SantaClawzzz/RCXD/Mechanics/Car/Front Wheels and Servo/Servo vasak kinnitus.step

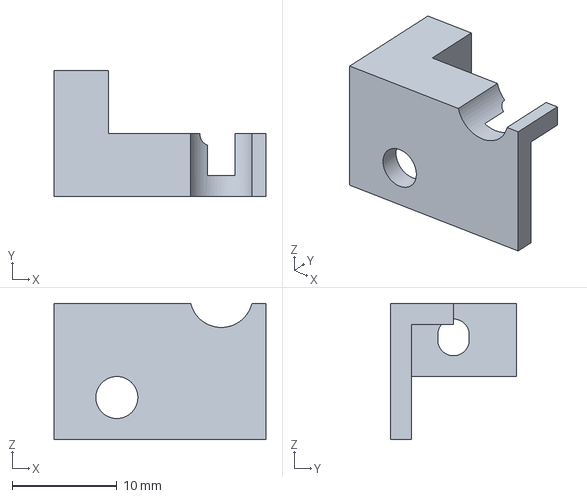
[picture p17: CAD file, 2026-05-07]
Mechanics/Car/Front Wheels and Servo/Servo vasak kinnitus.step
20.2 x 12.0 x 13.0 mm
