SantaClawzzz/RCXD/Mechanics/Car/Front Wheels and Servo/Servo liigend.step

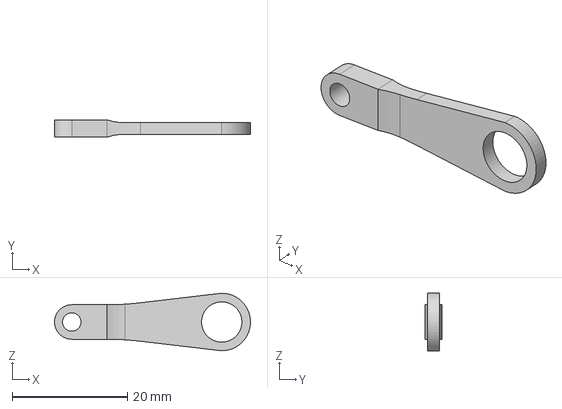
[picture p18: CAD file, 2026-05-07]
Mechanics/Car/Front Wheels and Servo/Servo liigend.step
34.0 x 3.00 x 10.0 mm
