SantaClawzzz/RCXD/Mechanics/Car/Front Wheels and Servo/Esiratta rumm.step

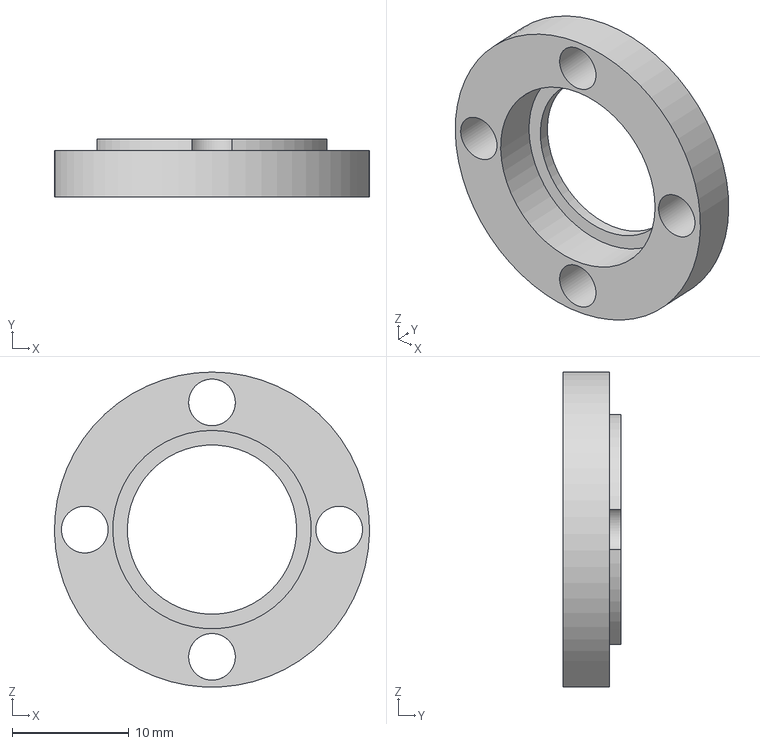
[picture p19: CAD file, 2026-05-07]
Mechanics/Car/Front Wheels and Servo/Esiratta rumm.step
27.0 x 5.00 x 27.0 mm
