SantaClawzzz/RCXD/Mechanics/Car/Front Wheels and Servo/Esiratta kork.step

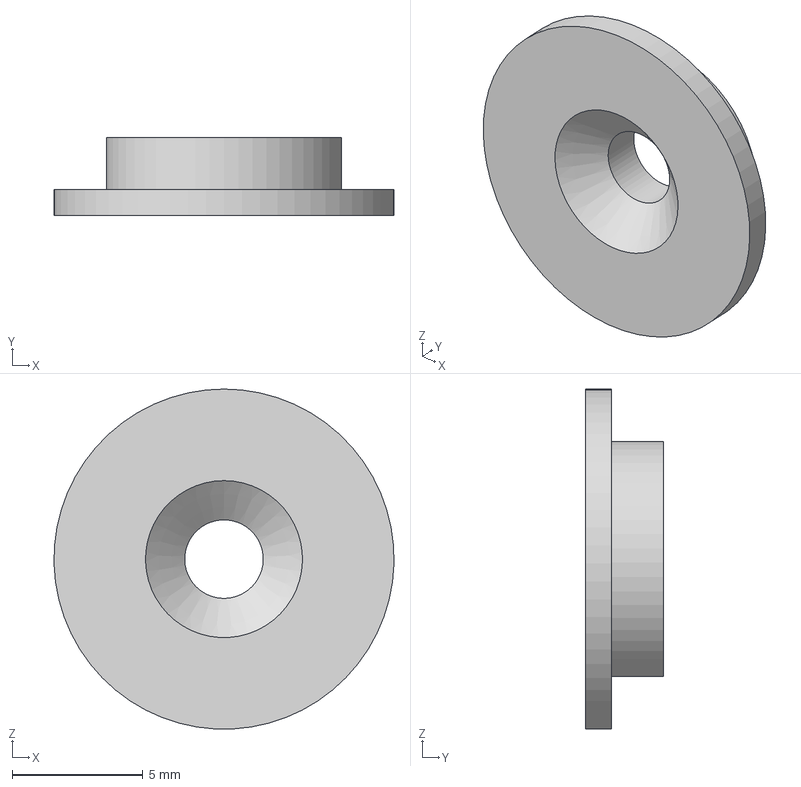
[picture p20: CAD file, 2026-05-07]
Mechanics/Car/Front Wheels and Servo/Esiratta kork.step
13.0 x 3.00 x 13.0 mm
