SantaClawzzz/RCXD/Mechanics/Car/Front Wheels and Servo/Servomootori kinnitus.step

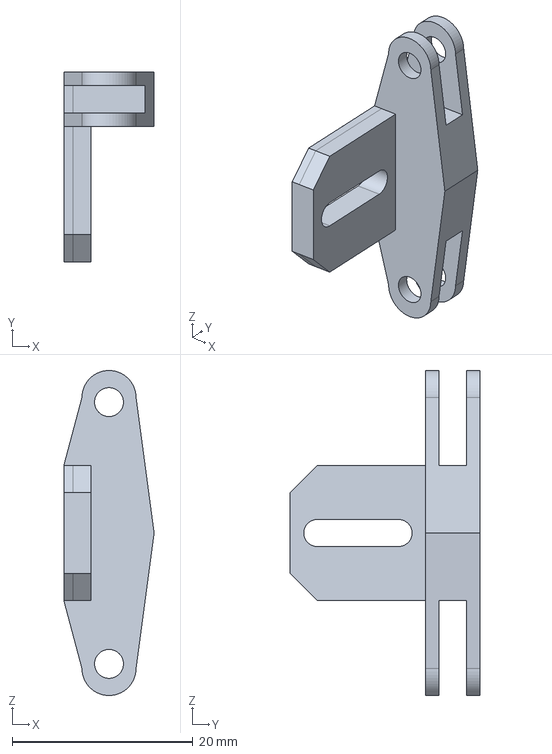
[picture p21: CAD file, 2026-05-07]
Mechanics/Car/Front Wheels and Servo/Servomootori kinnitus.step
10.00 x 21.0 x 36.0 mm
