SantaClawzzz/RCXD/Mechanics/Car/Front Wheels and Servo/Esiratas.step

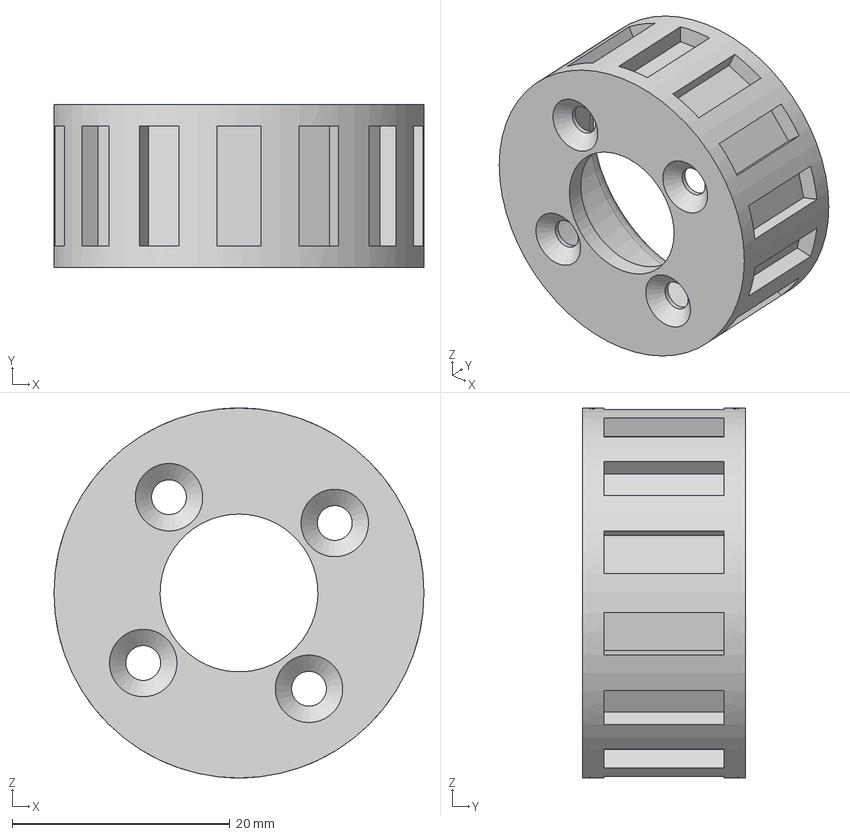
[picture p22: CAD file, 2026-05-07]
Mechanics/Car/Front Wheels and Servo/Esiratas.step
34.0 x 15.0 x 34.0 mm
