SantaClawzzz/RCXD/Mechanics/Car/Front Wheels and Servo/Rattarummi kinnitus.step

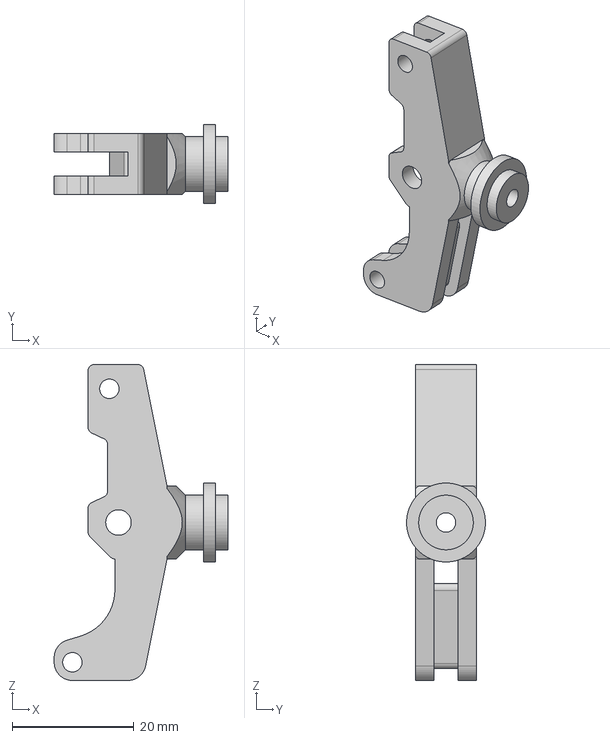
[picture p23: CAD file, 2026-05-07]
Mechanics/Car/Front Wheels and Servo/Rattarummi kinnitus.step
28.6 x 13.0 x 52.0 mm
