SantaClawzzz/RCXD/Mechanics/Car/Front Wheels and Servo/Esirataste hoidik.step

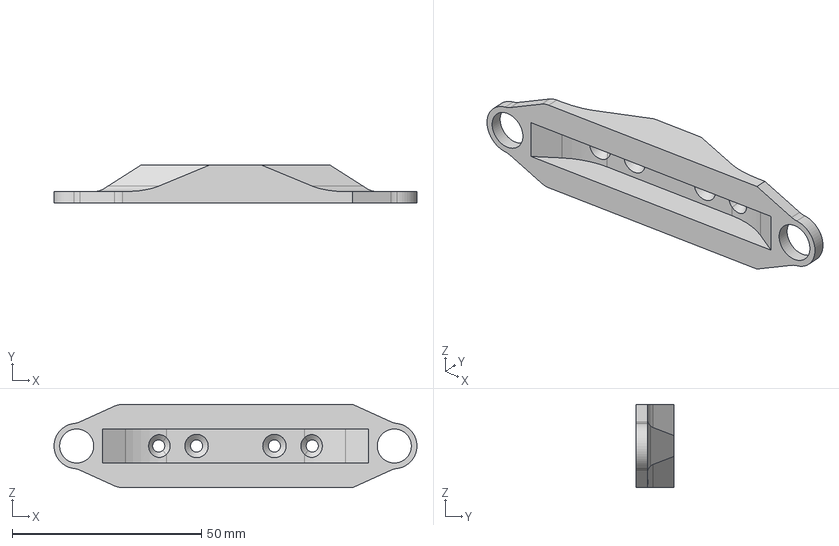
[picture p24: CAD file, 2026-05-07]
Mechanics/Car/Front Wheels and Servo/Esirataste hoidik.step
96.0 x 10.0 x 22.0 mm
