SantaClawzzz/RCXD/Electronics/RC-XD(RX)/RC-XD(RX).pdf

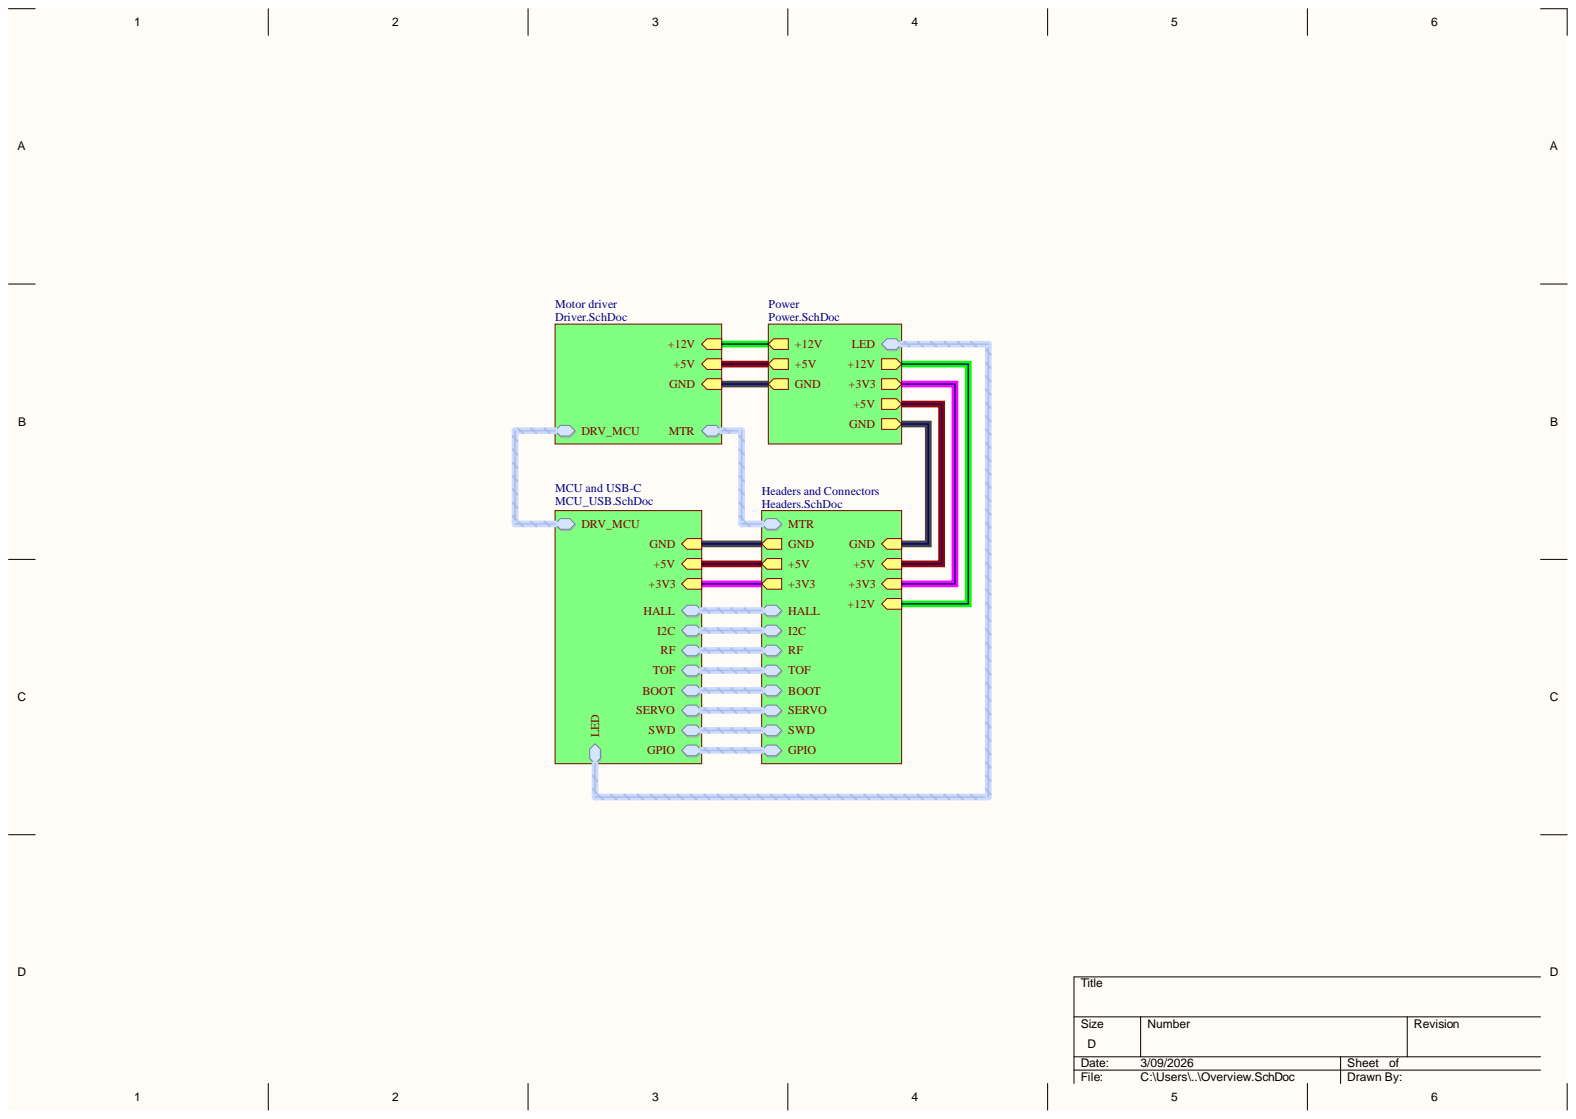
[picture p28: page 1]

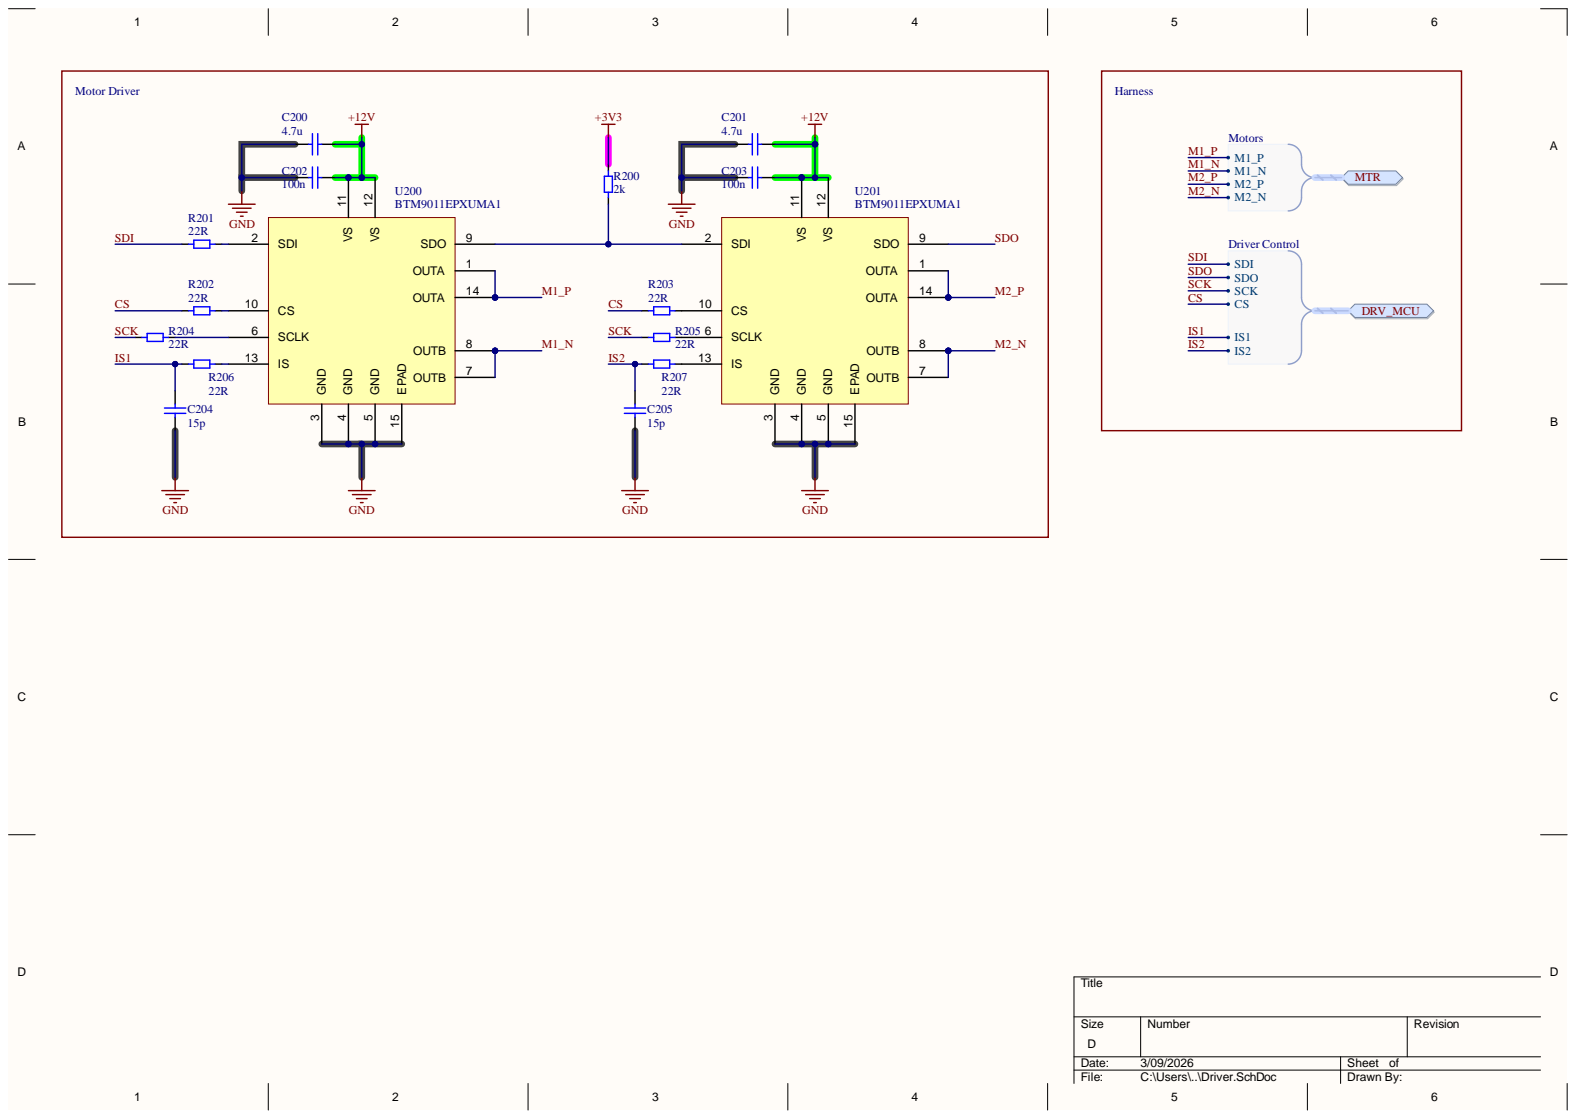
[picture p29: page 2]

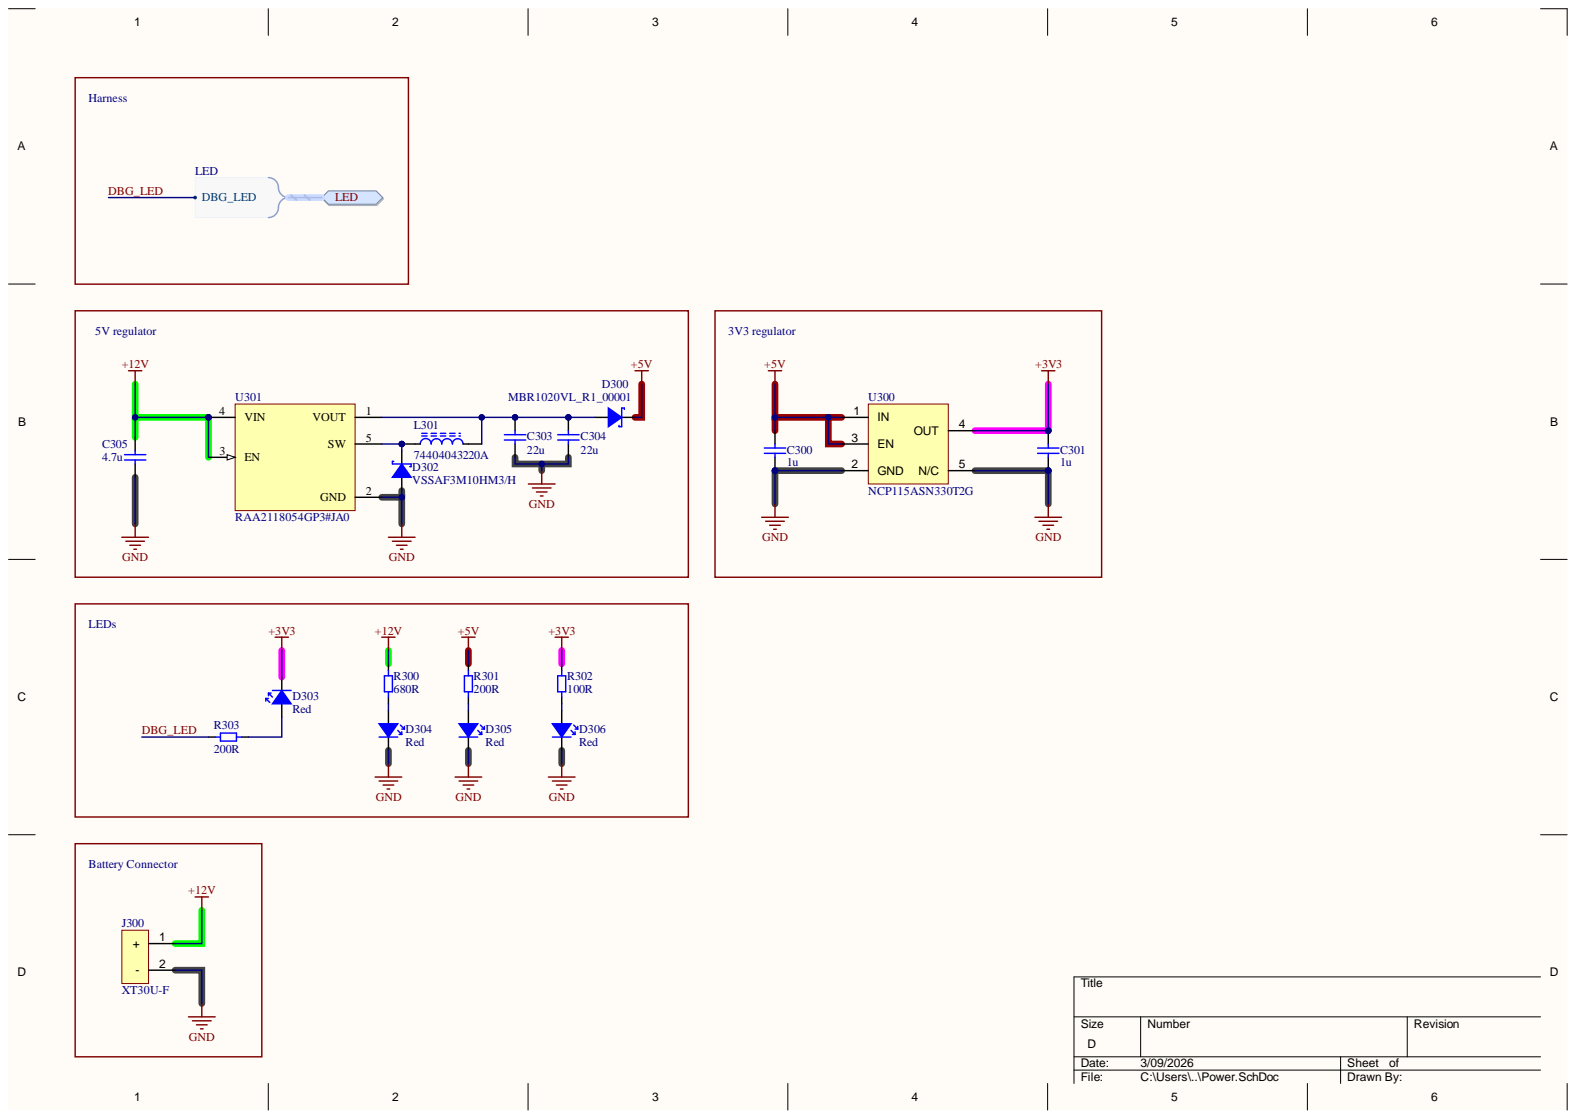
[picture p30: page 3]

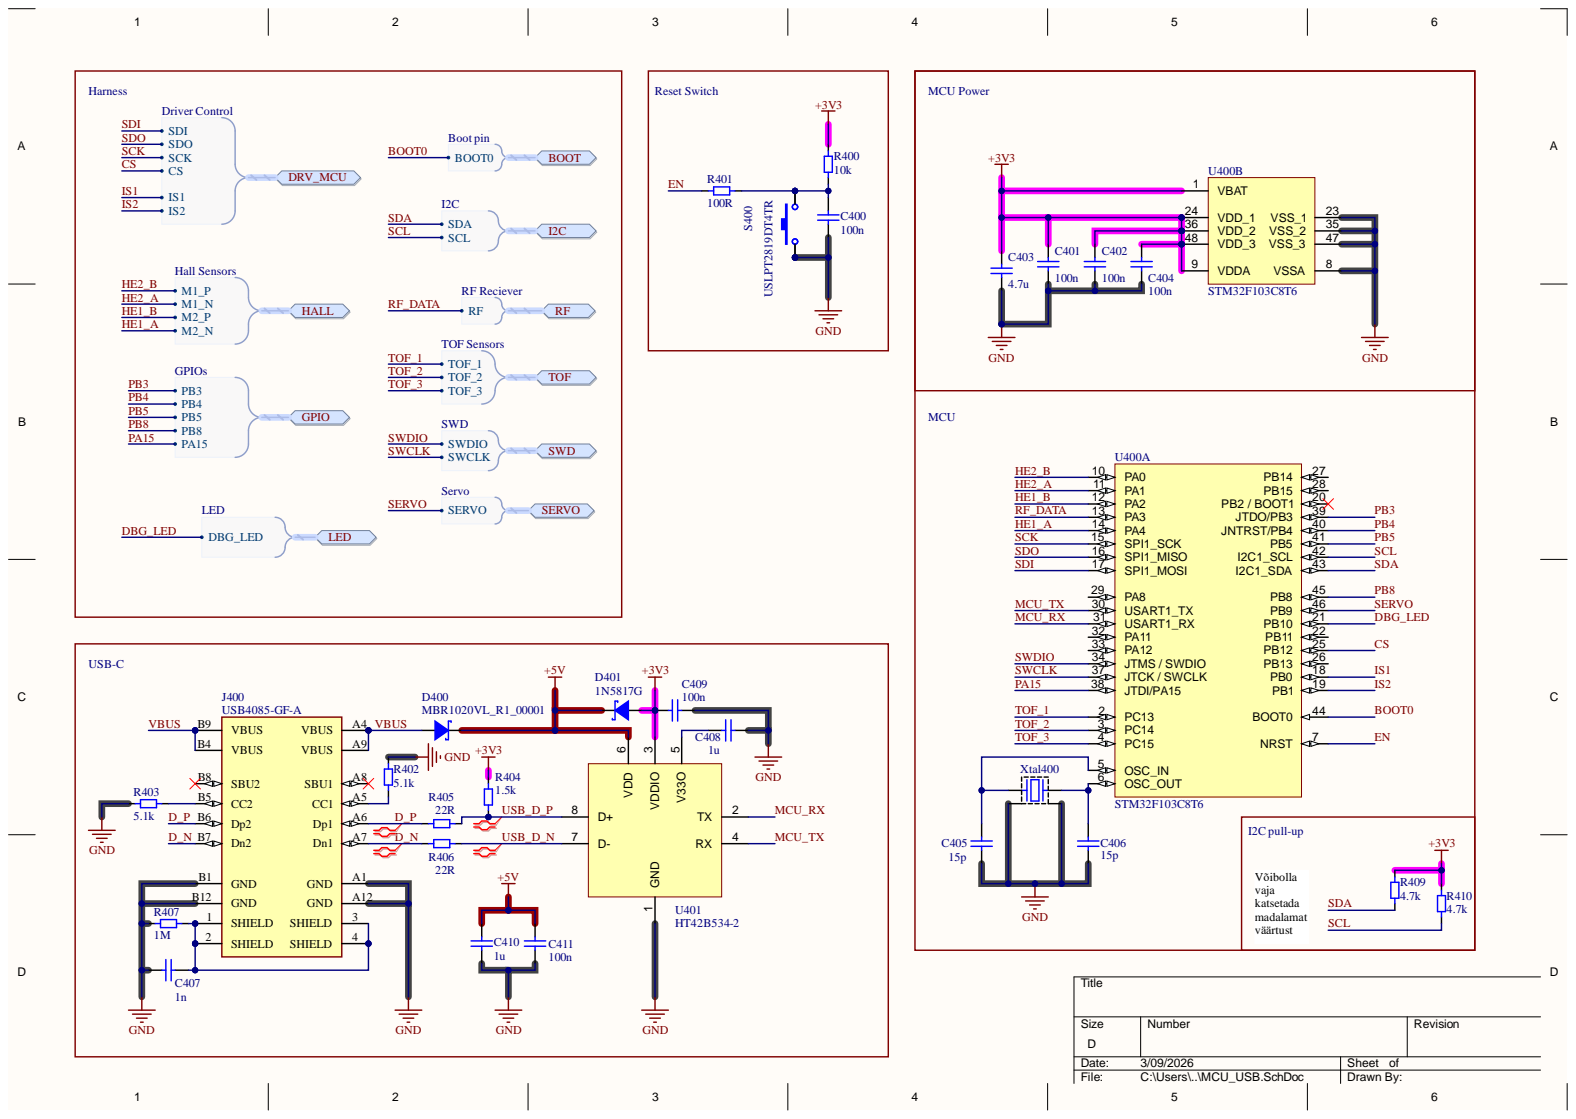
[picture p31: page 4]

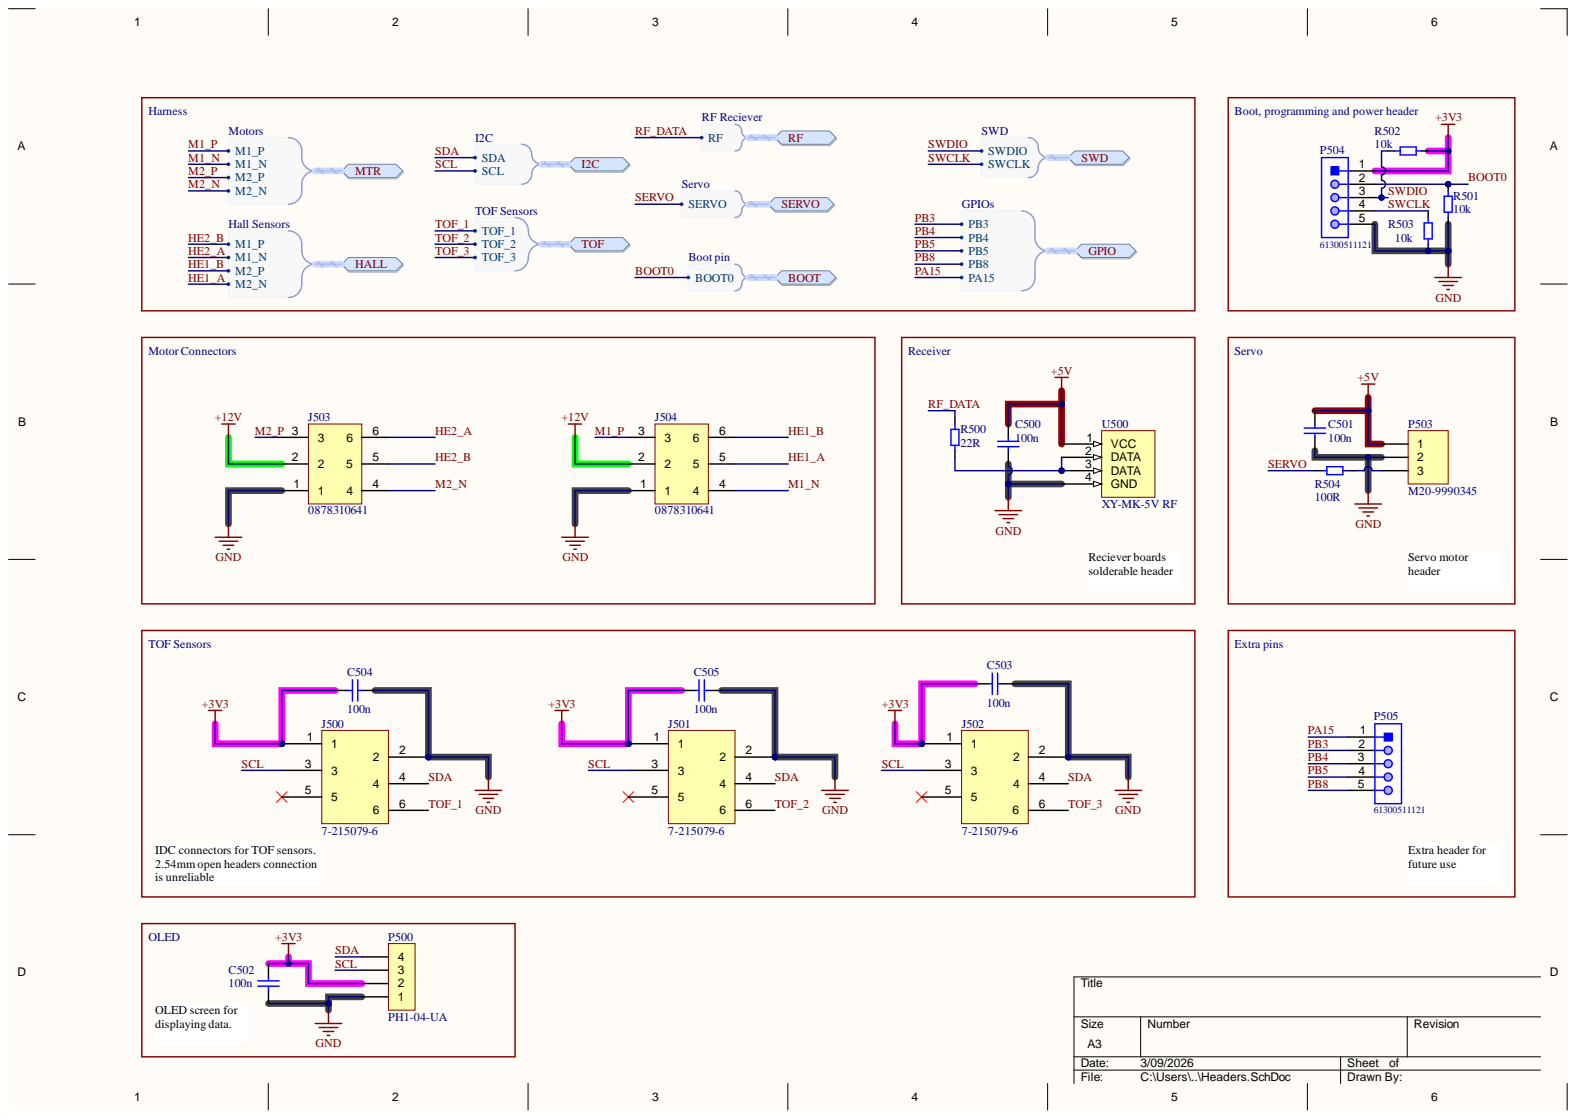
[picture p32: page 5]

Boot, programming and power header

IDC connectors for TOF sensors.
2.54mm open headers connection
is unreliable

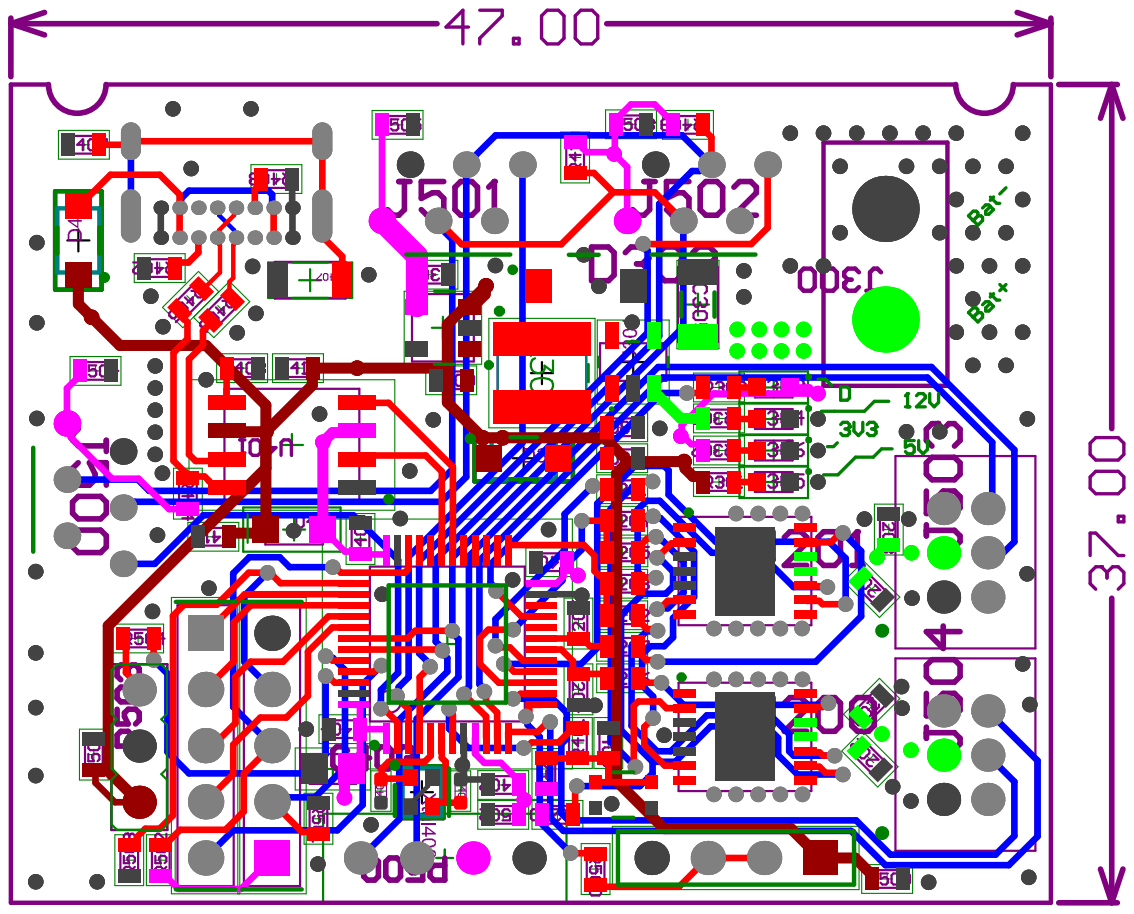
[picture p33: page 6]

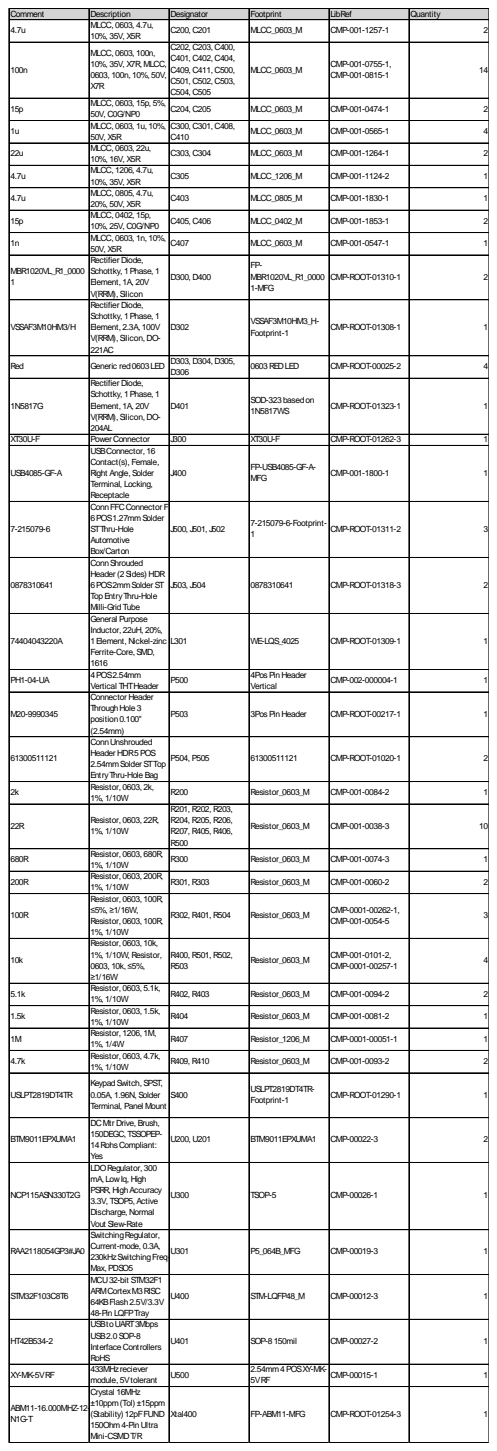
[picture p34: page 7]
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

15p | MLCC, 0603, 15p, 5%, 50V, C0G/NP0 | C204, C205 | MLCC_0603_M | CMP-001-0474-1 | 2

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

22u | MLCC, 0603, 22u, 10%, 16V, X5R | C303, C304 | MLCC_0603_M | CMP-001-1264-1 | 2

4.7u | MLCC, 1206, 4.7u, 10%, 35V, X5R | C305 | MLCC_1206_M | CMP-001-1124-2 | 1

4.7u | MLCC, 0805, 4.7u, 20%, 50V, X5R | C403 | MLCC_0805_M | CMP-001-1830-1 | 1

15p | MLCC, 0402, 15p, 10%, 25V, C0G/NP0 | C405, C406 | MLCC_0402_M | CMP-001-1853-1 | 2

1n | MLCC, 0603, 1n, 10%, 50V, X5R | C407 | MLCC_0603_M | CMP-001-0547-1 | 1

MBR1020VL_R1_0000 1 | Rectifier Diode, Schottky, 1Phase, 1 Element, 1A, 20V V(RRM), Silicon | D300, D400 | FP-MBR1020VL_R1_0000 1-MFG | CMP-ROOT-01310-1 | 2

VSSAF3M10HM3/H | Rectifier Diode, Schottky, 1Phase, 1 Element, 2.3A, 100V V(RRM), Silicon, DO-221AC | D302 | VSSAF3M10HM3_H-Footprint-1 | CMP-ROOT-01308-1 | 1

Red | Generic red0603LED | D303, D304, D305, D306 | 0603REDLED | CMP-ROOT-00025-2 | 4

1N5817G | Rectifier Diode, Schottky, 1Phase, 1 Element, 1A, 20V V(RRM), Silicon, DO-204AL | D401 | SOD-323basedon 1N5817WS | CMP-ROOT-01323-1 | 1

XT30U-F | Power Connector | J300 | XT30U-F | CMP-ROOT-01262-3 | 1
USB4085-GF-A | USBConnector, 16 Contact(s), Female, Right Angle, Solder Terminal, Locking, Receptacle | J400 | FP-USB4085-GF-A-MFG | CMP-001-1800-1 | 1

7-215079-6 | ConnFFCConnector F 6POS1.27mmSolder STThru-Hole Automotive Box/Carton | J500, J501, J502 | 7-215079-6-Footprint-1 | CMP-ROOT-01311-2 | 3

0878310641 | ConnShrouded Header (2Sides) HDR 6POS2mmSolder ST TopEntryThru-Hole Milli-Grid Tube | J503, J504 | 0878310641 | CMP-ROOT-01318-3 | 2

74404043220A | General Purpose Inductor, 22uH, 20%, 1Element, Nickel-zinc Ferrite-Core, SMD, 1616 | L301 | WE-LQS_4025 | CMP-ROOT-01309-1 | 1

PH1-04-UA | 4POS2.54mm Vertical THTHeader | P500 | 4PosPin Header Vertical | CMP-002-000004-1 | 1

M20-9990345 | Connector Header ThroughHole 3 position0.100" (2.54mm) | P503 | 3PosPin Header | CMP-ROOT-00217-1 | 1

61300511121 | ConnUnshrouded Header HDR5POS 2.54mmSolder STTop EntryThru-HoleBag | P504, P505 | 61300511121 | CMP-ROOT-01020-1 | 2

2k | Resistor, 0603, 2k, 1%, 1/10W | R200 | Resistor_0603_M | CMP-001-0084-2 | 1

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

680R | Resistor, 0603, 680R, 1%, 1/10W | R300 | Resistor_0603_M | CMP-001-0074-3 | 1

200R | Resistor, 0603, 200R, 1%, 1/10W | R301, R303 | Resistor_0603_M | CMP-001-0060-2 | 2

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

1.5k | Resistor, 0603, 1.5k, 1%, 1/10W | R404 | Resistor_0603_M | CMP-001-0081-2 | 1

1M | Resistor, 1206, 1M, 1%, 1/4W | R407 | Resistor_1206_M | CMP-0001-00051-1 | 1

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

BTM9011EPXUMA1 | DCMtr Drive, Brush, 150DEGC, TSSOPEP-14RohsCompliant: Yes | U200, U201 | BTM9011EPXUMA1 | CMP-00022-3 | 2

NCP115ASN330T2G | LDORegulator, 300 mA, LowIq, High PSRR, HighAccuracy 3.3V, TSOP5, Active Discharge, Normal Vout Slew-Rate | U300 | TSOP-5 | CMP-00026-1 | 1

RAA2118054GP3#JA0 | SwitchingRegulator, Current-mode, 0.3A, 230kHzSwitchingFreq-Max, PDSO5 | U301 | P5_064B_MFG | CMP-00019-3 | 1

STM32F103C8T6 | MCU32-bit STM32F1 ARMCortexM3RISC 64KBFlash2.5V/3.3V 48-Pin LQFPTray | U400 | STM-LQFP48_M | CMP-00012-3 | 1

HT42B534-2 | USBtoUART3Mbps USB2.0SOP-8 Interface Controllers RoHS | U401 | SOP-8150mil | CMP-00027-2 | 1

XY-MK-5VRF | 433MHzreciever module, 5Vtolerant | U500 | 2.54mm4POSXY-MK-5VRF | CMP-00015-1 | 1

ABM11-16.000MHZ-12-N1G-T | Crystal 16MHz ±10ppm(Tol) ±15ppm (Stability) 12pFFUND 150Ohm4-Pin Ultra Mini-CSMDT/R | Xtal400 | FP-ABM11-MFG | CMP-ROOT-01254-3 | 1
