SantaClawzzz/RCXD/Software/RX_C6/Core/Inc/ibus.h

/*
 * flysky_ibus.h
 *
 *  Created on: Feb 4, 2021
 *      Author: mokhwasomssi
 */


#ifndef __IBUS_H__
#define __IBUS_H__


#include "main.h"
#include <stdbool.h>


/* User configuration */
#define IBUS_UART				(&huart1)
#define IBUS_USER_CHANNELS		7		// Use 7 channels (CH7 = lock switch)


/* Defines */
#define IBUS_LENGTH				0x20	// 32 bytes
#define IBUS_COMMAND40			0x40	// Command to set servo or motor speed is always 0x40
#define IBUS_MAX_CHANNLES		14


/* Main Functions */
void ibus_init();
bool ibus_read(uint16_t* ibus_data);


/* Sub Functions */
bool ibus_is_valid();
bool ibus_checksum();
void ibus_update(uint16_t* ibus_data);
void ibus_soft_failsafe(uint16_t* ibus_data, uint8_t fail_safe_max);
void ibus_reset_failsafe();

#endif /* __IBUS_H__ */
